OpenSourceEBike/Automatic_Switch_Anti_spark_JBD_BMS/documentation/board_02.jpg

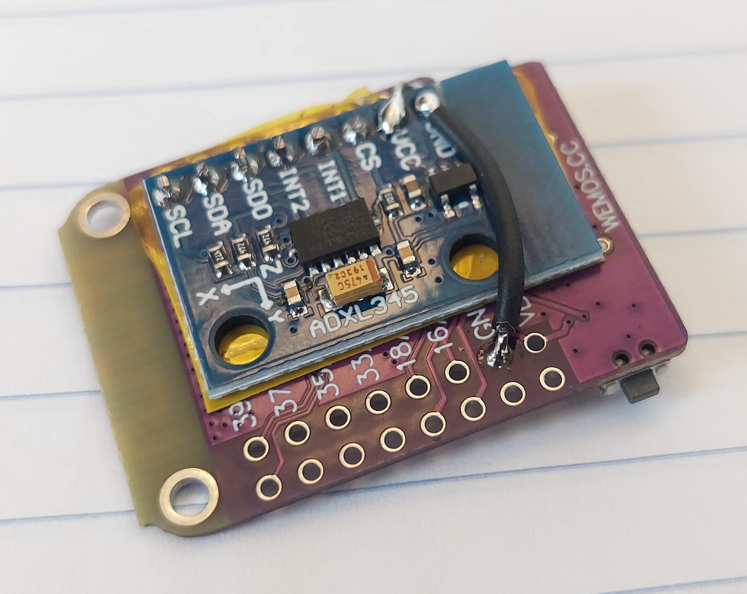
documentation/board_02.jpg
