OpenSourceEBike/Automatic_Switch_Anti_spark_JBD_BMS/documentation/firmware.png

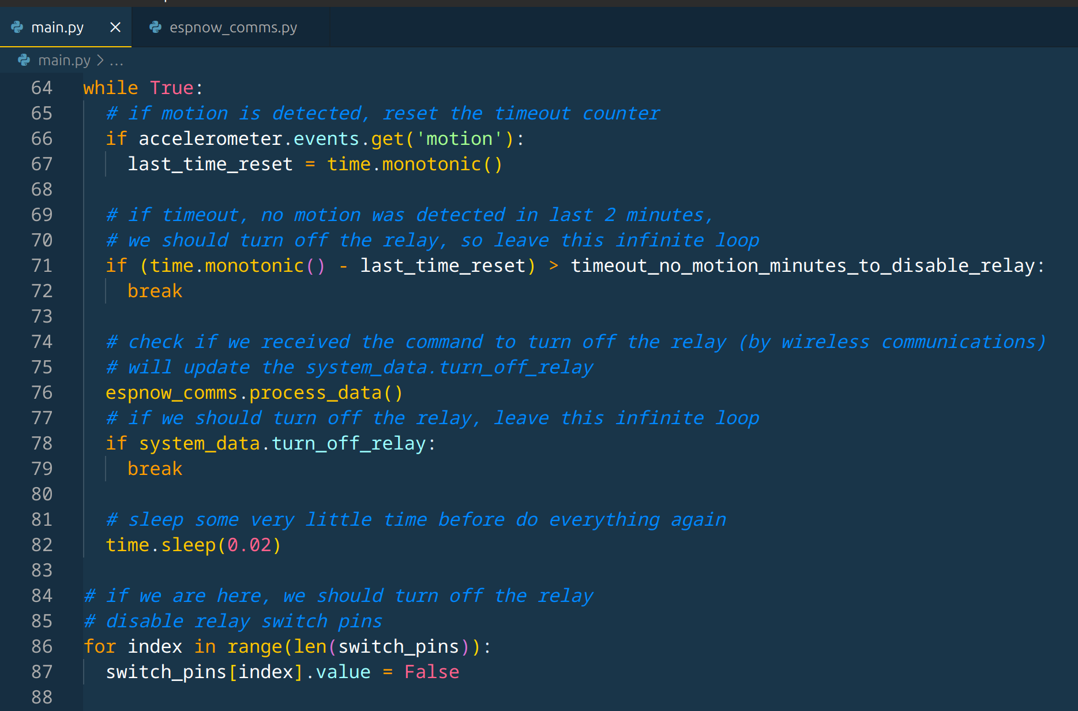
documentation/firmware.png
