OpenSourceEBike/Automatic_Switch_Anti_spark_JBD_BMS/hardware/schematic.kicad_sch

## KiCad design hardware/schematic.kicad_sch (2023-07-03)

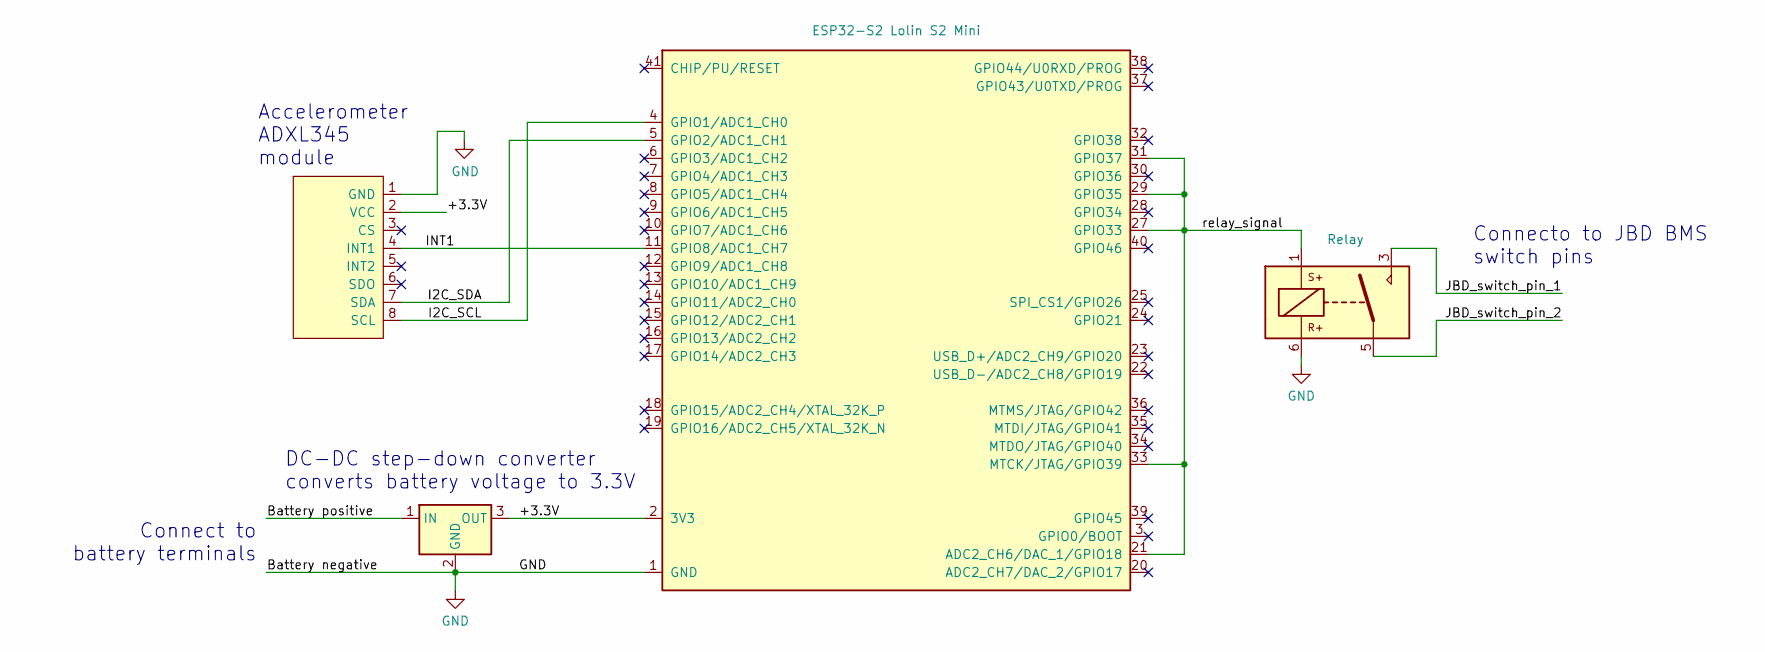
[picture p14: schematic schematic.kicad_sch]

Parts:
K1: Relay; Relay_1P1T_NO_10x24x18.8mm_Panasonic_ADW11xxxxW_THT
U1: Step-down converter to 3.3V; Converter_DCDC_Murata_OKI-78SR_Vertical

Connections:
+3.3V: U1.3 (OUT)
Battery positive: U1.1 (IN)
GND: K1.6, U1.2 (GND)
JBD_switch_pin_1: K1.3
JBD_switch_pin_2: K1.5
relay_signal: K1.1

Notes on the sheet:
Connecto to JBD BMS switch pins
Accelerometer ADXL345 module
Connect to battery terminals
DC-DC step-down converter converts battery voltage to 3.3V
